LifeAtTerminalVelocity/RSLPin_TemporaryPin/STL/RSL Pin Holder v5.stl

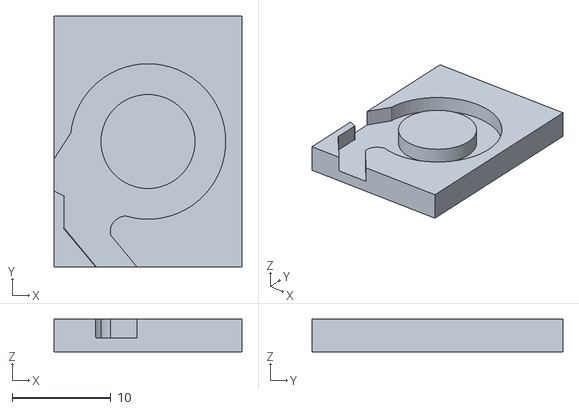
[picture p18: CAD file, 2025-05-05, an earlier design]
STL/RSL Pin Holder v5.stl
19.1 x 25.4 x 3.31
