LifeAtTerminalVelocity/RSLPin_TemporaryPin/img/V9.6Long_Build_process_6.jpeg

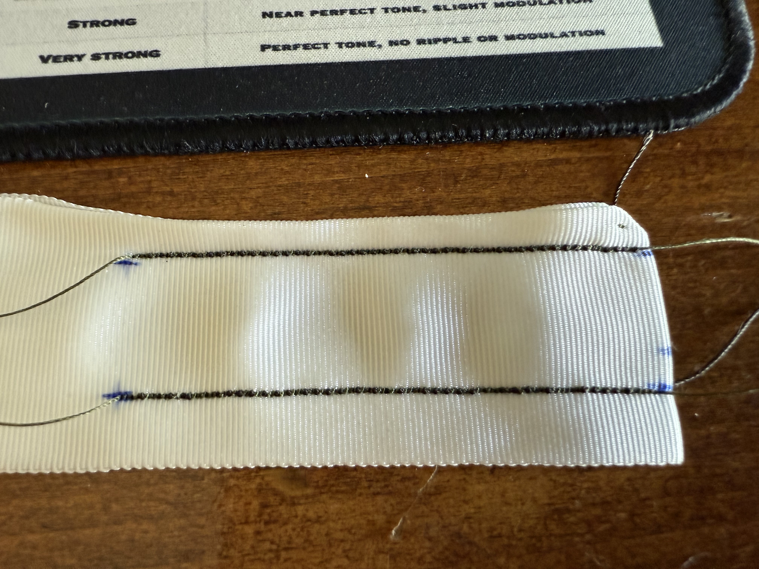
img/V9.6Long_Build_process_6.jpeg
