LifeAtTerminalVelocity/RSLPin_TemporaryPin/img/v6_finished1.jpeg

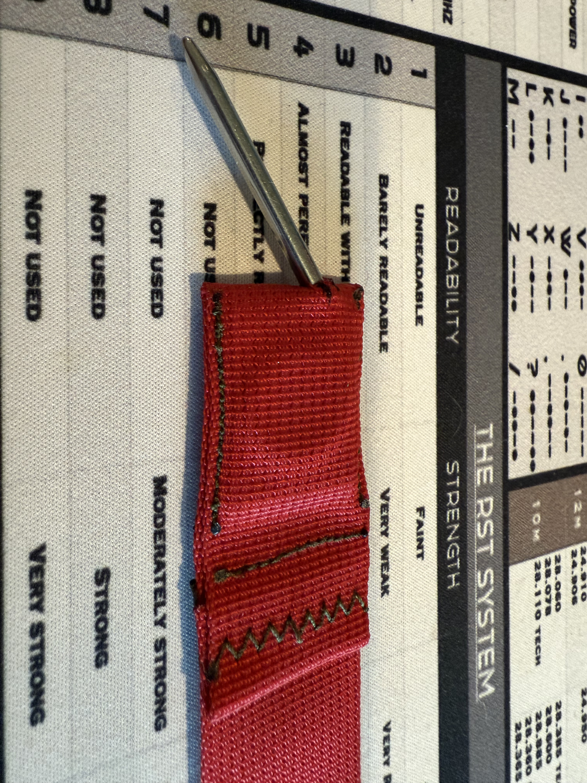
img/v6_finished1.jpeg
