LifeAtTerminalVelocity/RSLPin_TemporaryPin/img/v7comparedtov6.jpeg

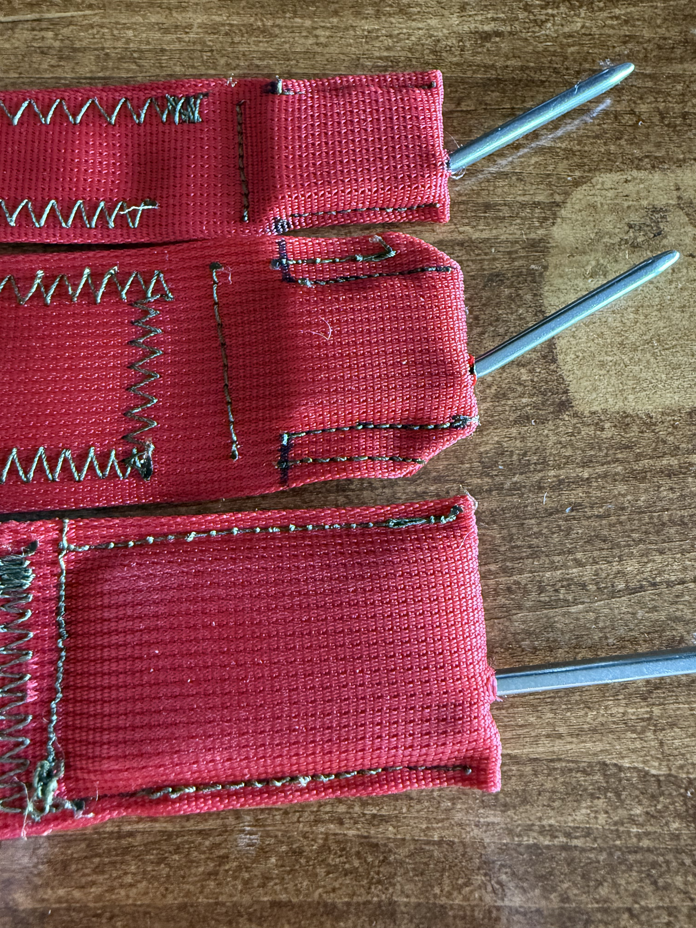
img/v7comparedtov6.jpeg
