LifeAtTerminalVelocity/RSLPin_TemporaryPin/img/ZigZagDetail.jpeg

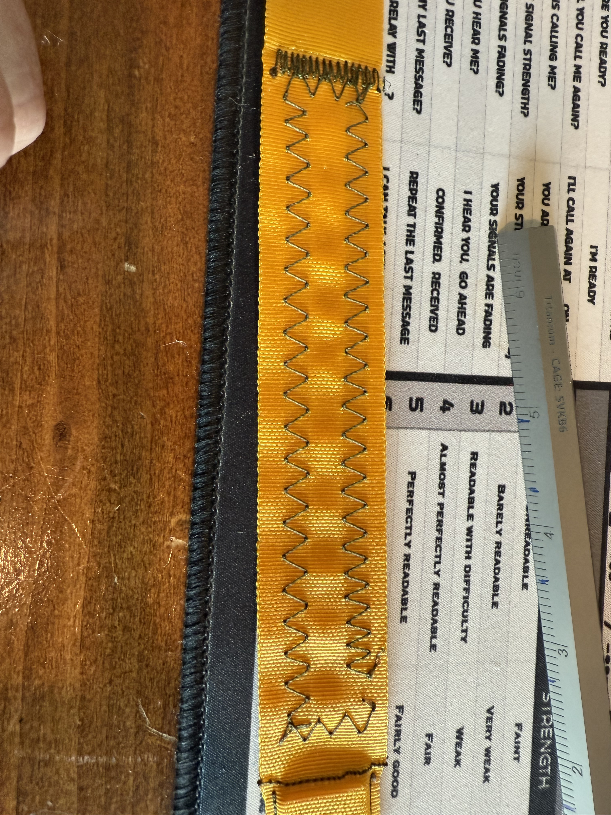
img/ZigZagDetail.jpeg
